audyakbar4/SafeGuard-Nano/3D Design/Dari Atas.png

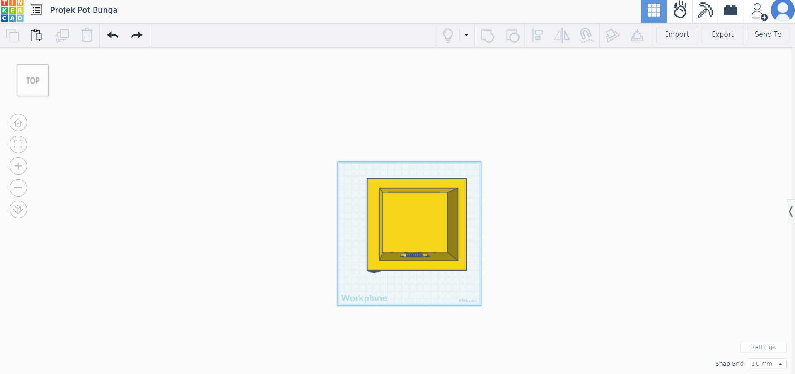
3D Design/Dari Atas.png
