audyakbar4/SafeGuard-Nano/3D Design/Dari Bawah.png

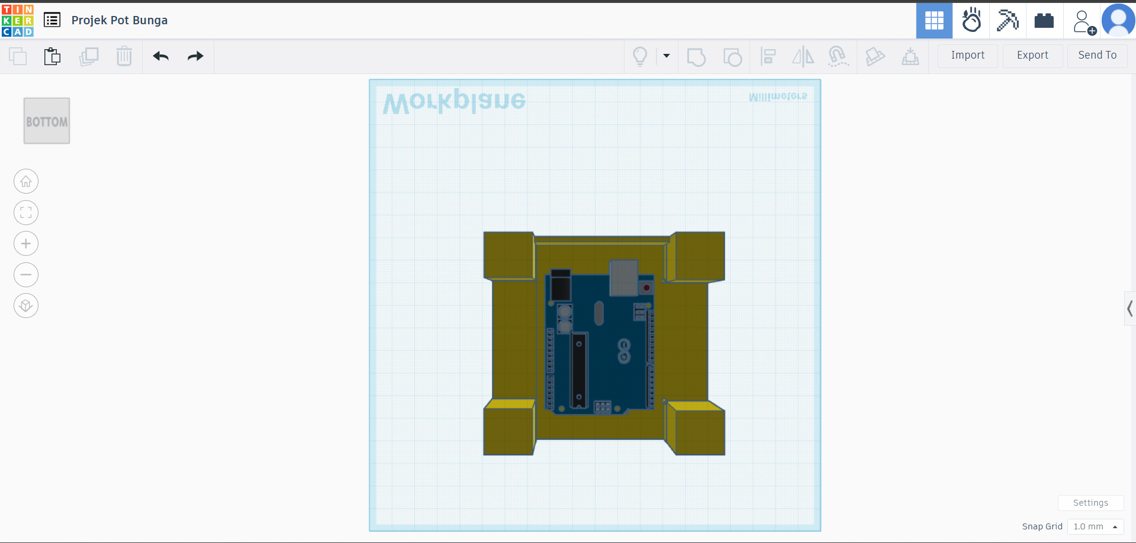
3D Design/Dari Bawah.png
