audyakbar4/SafeGuard-Nano/3D Design/Dari Kanan.png

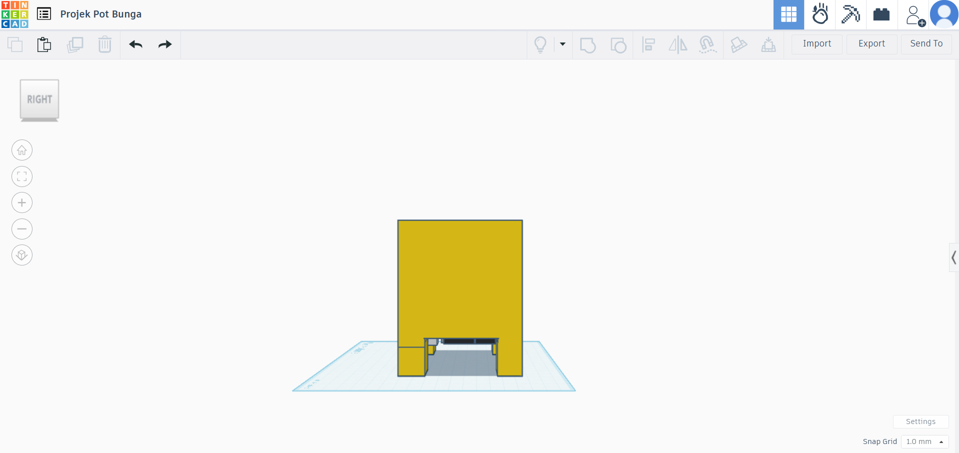
3D Design/Dari Kanan.png
