audyakbar4/SafeGuard-Nano/3D Design/POT 2/Back.png

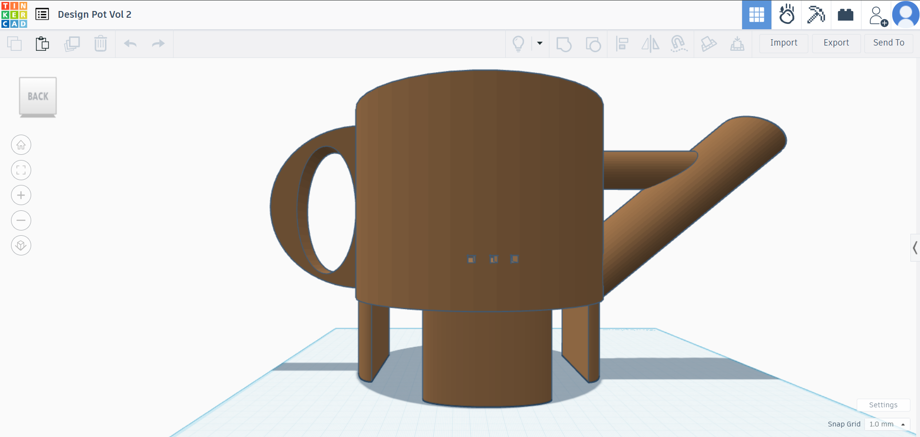
3D Design/POT 2/Back.png
