audyakbar4/SafeGuard-Nano/3D Design/POT 2/Bottom.png

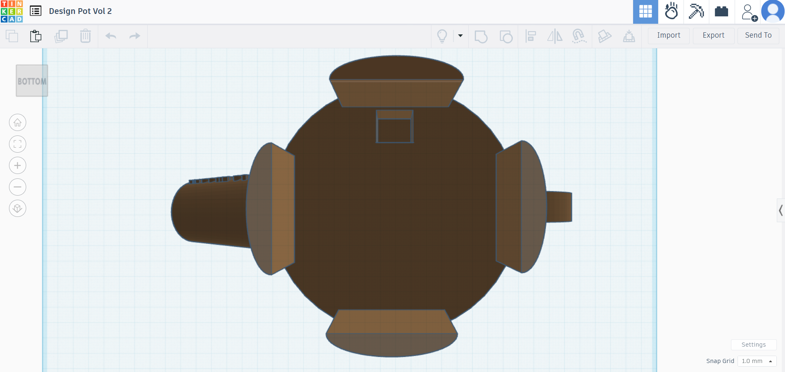
3D Design/POT 2/Bottom.png
