audyakbar4/SafeGuard-Nano/3D Design/POT 2/Front.png

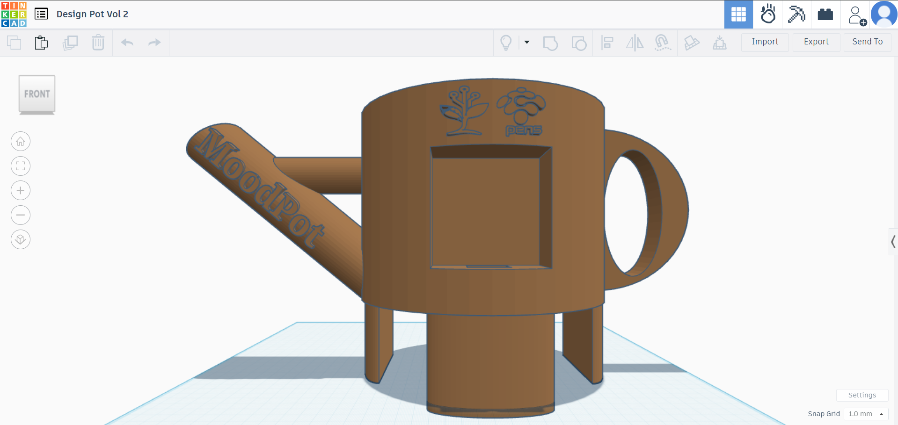
3D Design/POT 2/Front.png
