audyakbar4/SafeGuard-Nano/3D Design/POT 2/Top.png

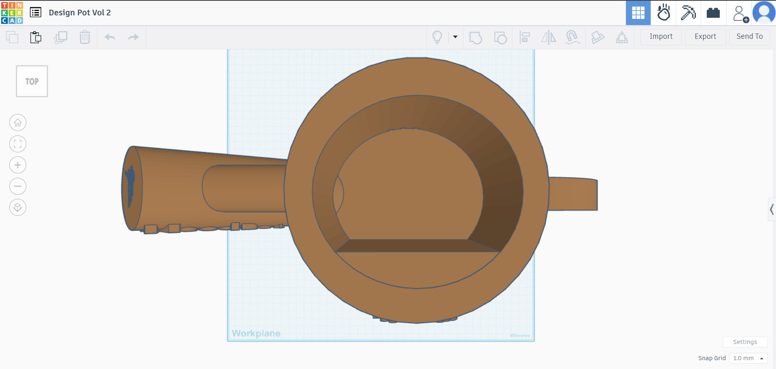
3D Design/POT 2/Top.png
