audyakbar4/SafeGuard-Nano/Assets/Face Indicator/flat.png

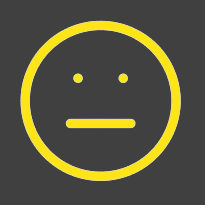
Assets/Face Indicator/flat.png
