audyakbar4/SafeGuard-Nano/Assets/Face Indicator/sad.png

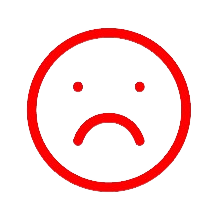
Assets/Face Indicator/sad.png
