audyakbar4/SafeGuard-Nano/Assets/Face Indicator/smile.png

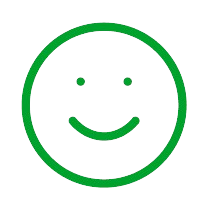
Assets/Face Indicator/smile.png
