audyakbar4/SafeGuard-Nano/Assets/Gambar/22841_1b-removebg-preview.png

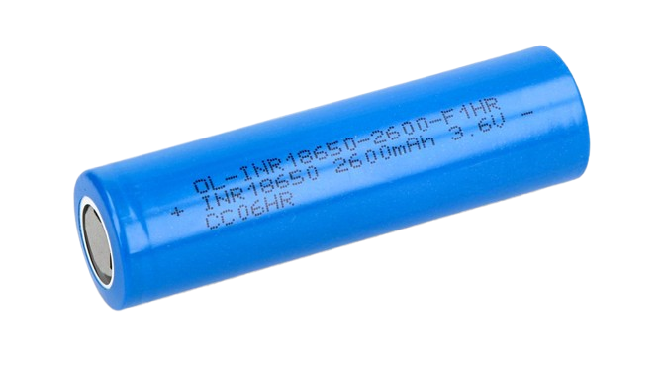
Assets/Gambar/22841_1b-removebg-preview.png
