audyakbar4/SafeGuard-Nano/Assets/Gambar/ArduinoUNOR3MicrocontrollerATMega328PDevelopmentBoardharishprojects_72-removebg-preview.png

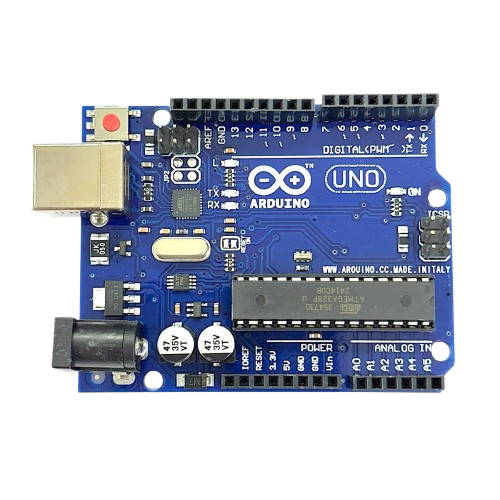
Assets/Gambar/ArduinoUNOR3MicrocontrollerATMega328PDevelopmentBoardharishprojects_72-removebg-preview.png
