audyakbar4/SafeGuard-Nano/Assets/Gambar/Bagsssan SafeGuard.png

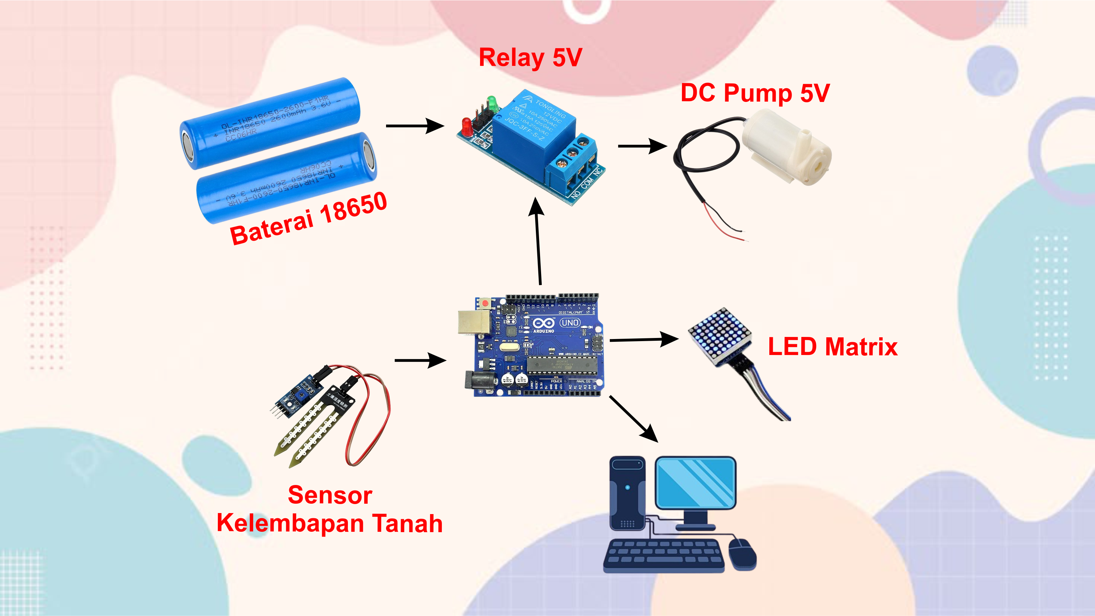
Assets/Gambar/Bagsssan SafeGuard.png
