audyakbar4/SafeGuard-Nano/Assets/Gambar/cIvz5HZaz0M9bmKr-image-1708447520994-removebg-preview.png

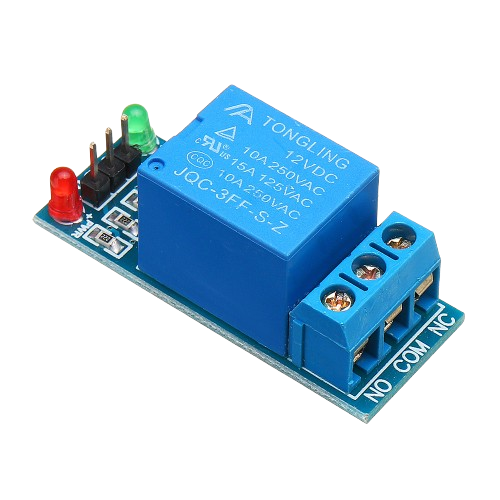
Assets/Gambar/cIvz5HZaz0M9bmKr-image-1708447520994-removebg-preview.png
