audyakbar4/SafeGuard-Nano/Assets/Gambar/d8a306eb-18e2-4c9e-a867-1908d567a8d3-removebg-preview.png

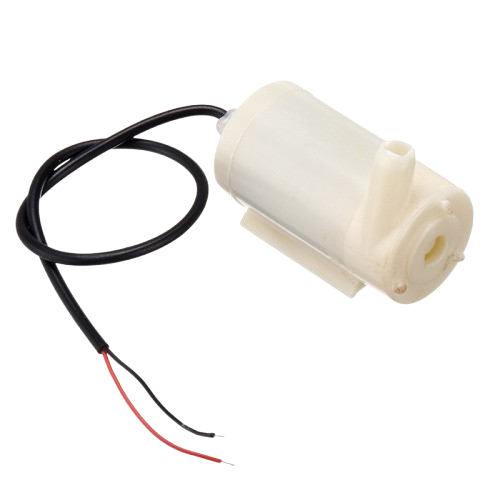
Assets/Gambar/d8a306eb-18e2-4c9e-a867-1908d567a8d3-removebg-preview.png
