audyakbar4/SafeGuard-Nano/Assets/Gambar/e1a2af799c2cfd85c5e895e72084e2d6.jpg

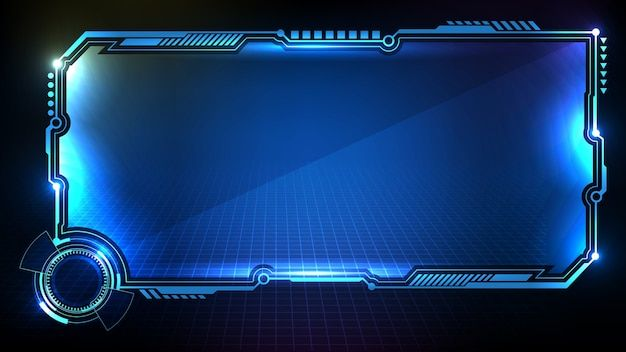
Assets/Gambar/e1a2af799c2cfd85c5e895e72084e2d6.jpg
