audyakbar4/SafeGuard-Nano/Assets/Gambar/imasssges-removebg-preview.png

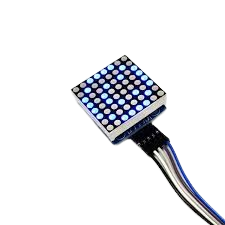
Assets/Gambar/imasssges-removebg-preview.png
