audyakbar4/SafeGuard-Nano/Assets/Gambar/sensor-kelembaban-tanah-removebg-preview.png

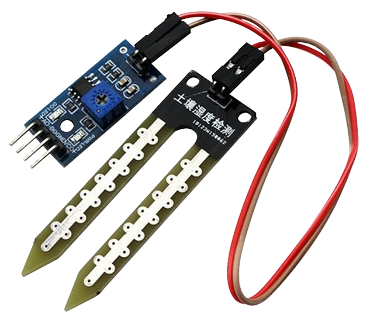
Assets/Gambar/sensor-kelembaban-tanah-removebg-preview.png
