audyakbar4/SafeGuard-Nano/Assets/Gambar/WhatsApp_Image_2025-04-25_at_20.21.20-removebg-preview.png

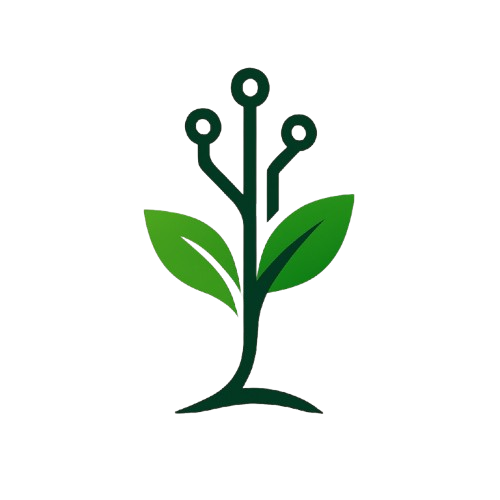
Assets/Gambar/WhatsApp_Image_2025-04-25_at_20.21.20-removebg-preview.png
