audyakbar4/SafeGuard-Nano/PCB Design/Tampak Luar.jpg

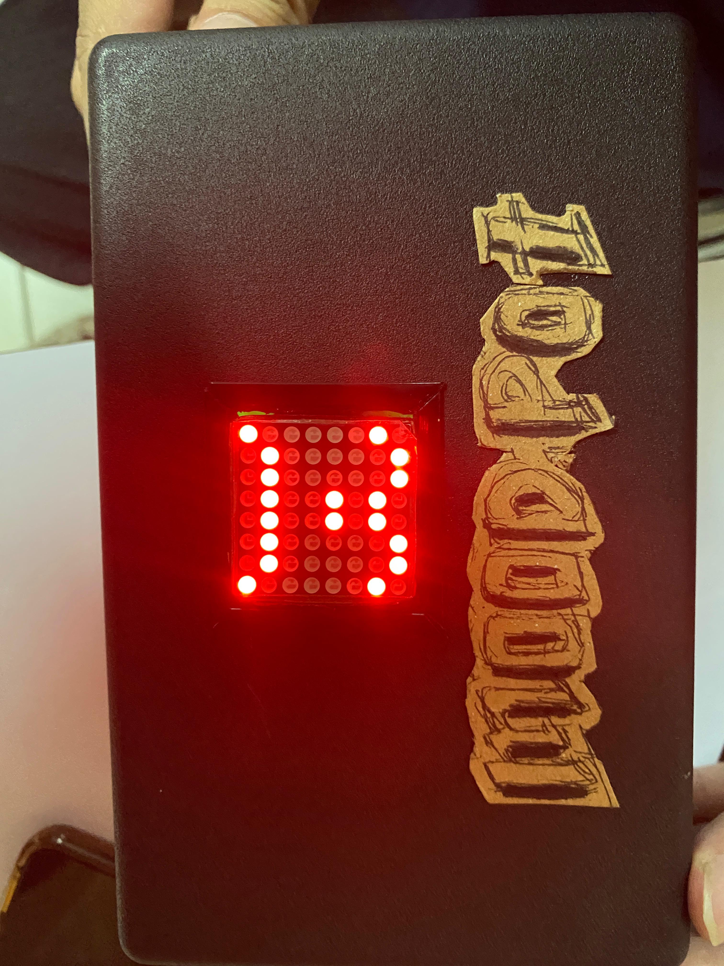
PCB Design/Tampak Luar.jpg
