audyakbar4/SafeGuard-Nano/UI-UX Design/About.png

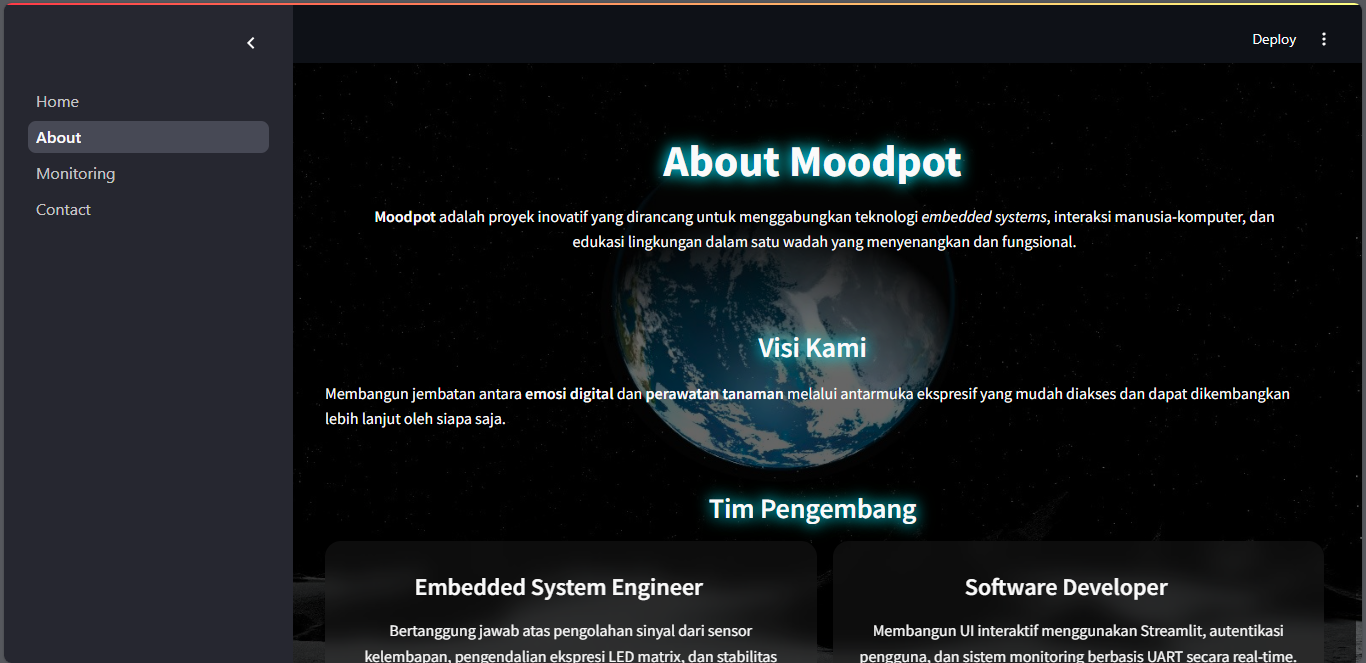
UI-UX Design/About.png
