audyakbar4/SafeGuard-Nano/UI-UX Design/Home.png

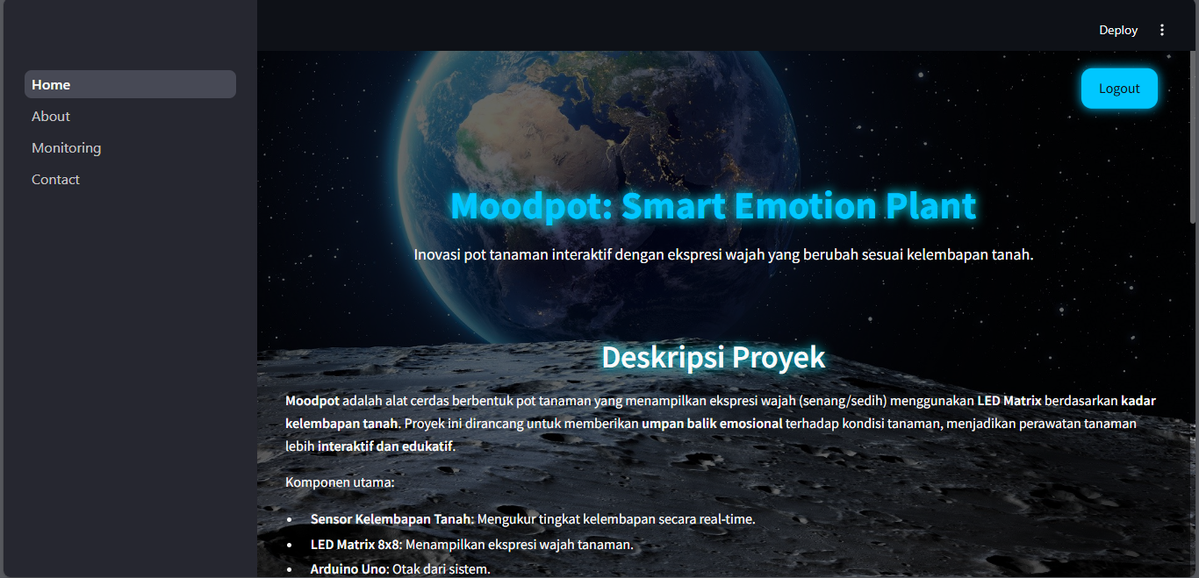
UI-UX Design/Home.png
