audyakbar4/SafeGuard-Nano/UI-UX Design/Monitoring1.png

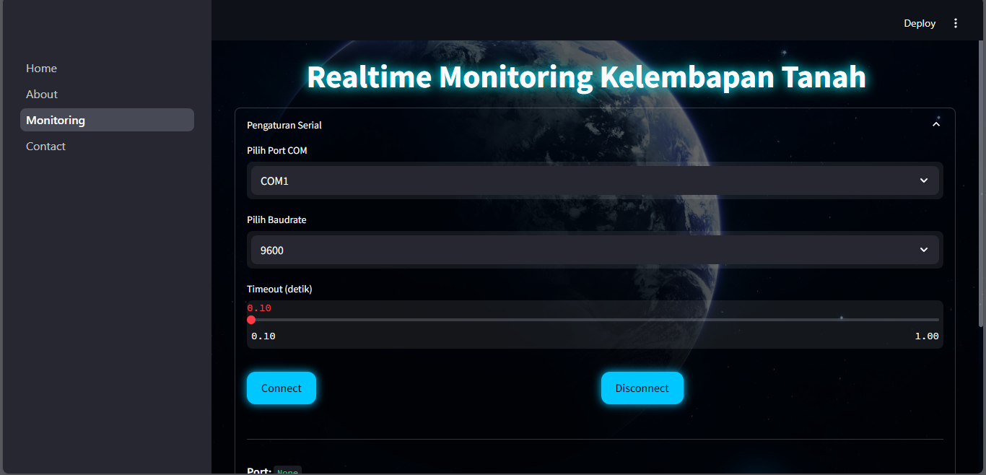
UI-UX Design/Monitoring1.png
