audyakbar4/SafeGuard-Nano/UI-UX Design/Register.png

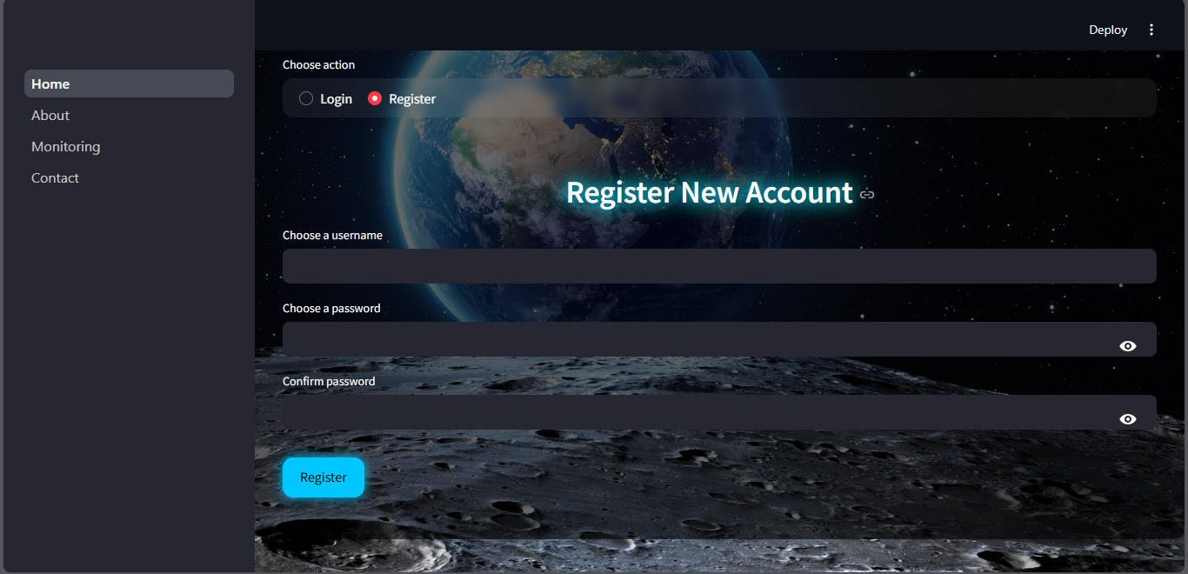
UI-UX Design/Register.png
