audyakbar4/SafeGuard-Nano/Source Code/src/spi.c

#include <avr/io.h>
#include "spi.h"

void spi_init() {
    DDRB |= (1 << PB3) | (1 << PB5) | (1 << PB2); // MOSI, SCK, SS as output
    SPCR = (1 << SPE) | (1 << MSTR) | (1 << SPR0); // Enable SPI, Master, f/16
}

void spi_send(uint8_t data) {
    SPDR = data;
    while (!(SPSR & (1 << SPIF)));
}
